oelprinz-org/BL49/software/BL49/BL49/board/board.h

/*
 * board.h
 *
 * Created: 23.05.2022 16:27:08
 *  Author: Heinrich
 */ 


#ifndef BOARD_H_
#define BOARD_H_

#include <avr/io.h>
#include <stdint.h>
#include <stdbool.h>

typedef enum
{
	LOW
	, HIGH
} tInputState;

typedef enum
{
	ON
	, OFF
} tLedState;

typedef struct 
{
	tInputState input1_state;
	tInputState input2_state;
} tBoard;

void board_init (tBoard *board);
void board_read_inputs (tBoard *board);
bool isActive (void);
void led1_toggle (void);
void led2_toggle (void);
void led1_setState (tLedState state);
void led2_setState (tLedState state);

#endif /* BOARD_H_ */
