oelprinz-org/BL49/software/BL49/BL49/cj125/cj125_registers.h

/*
 * cj125_registers.h
 *
 * Created: 22.05.2022 23:51:20
 *  Author: Heinrich
 */ 


#ifndef CJ125_REGISTERS_H_
#define CJ125_REGISTERS_H_

// cj125 registers
#define CJ125_RD_IDENT				0x4800	/* Identify request, gives revision of the chip. */
#define CJ125_RD_INIT1				0x6C00 	/* Requests the first init register. */
#define CJ125_RD_DIAG				0x7800	/* Dignostic request, gives the current status. */
#define CJ125_RD_INIT2				0x7E00  /* Requests the second init register. */

// return mode in init1 register
#define CJ125_RD_MODE_CAL			0x289D  /* The response of the init register when in calibration mode. */
#define CJ125_RD_MODE_V8			0x2888  /* The response of the init register when V=8 amplification is in use. */
#define CJ125_RD_MODE_V17			0x2889	/* The response of the init register when V=17 amplification is in use. */

// set mode:
#define CJ125_WR_SRESET				0x5A40	/* Software-RESET of SPI and all registers */ 
#define CJ125_WR_SRESET_END			0x5A00	/* Default value of init2 register */ 
#define CJ125_WR_MODE_CAL			0x569D  /* Sets the first init register in calibration mode. */
#define CJ125_WR_MODE_V8			0x5688  /* Sets the first init register in operation mode. V=8 amplification. */
#define CJ125_WR_MODE_V17			0x5689  /* Sets the first init register in operation mode. V=17 amplification. */

// diag register status:
#define CJ125_DIAG_REG_STATUS_OK        0xFF  /* The response of the diagnostic register when everything is ok. */
#define CJ125_DIAG_REG_STATUS_NOPOWER   0x55  /* The response of the diagnostic register when power is low. */
#define CJ125_DIAG_REG_STATUS_NOSENSOR  0x7F  /* The response of the diagnostic register when no sensor is connected. */

#define CJ125_DIAG_MASK					0x3		// we need only two bits from diag register...
#define CJ125_IDENT_MASK				0xF0	// mask for ident register, after masking the value should by 0x60

#define CJ125_DIAG_INSTR_F				0
#define CJ125_DIAG_PARITY				1
#define CJ125_DIAG_R_W					2

#endif /* CJ125_REGISTERS_H_ */
